CynixPub/CyMouse/assets/3d_board.png

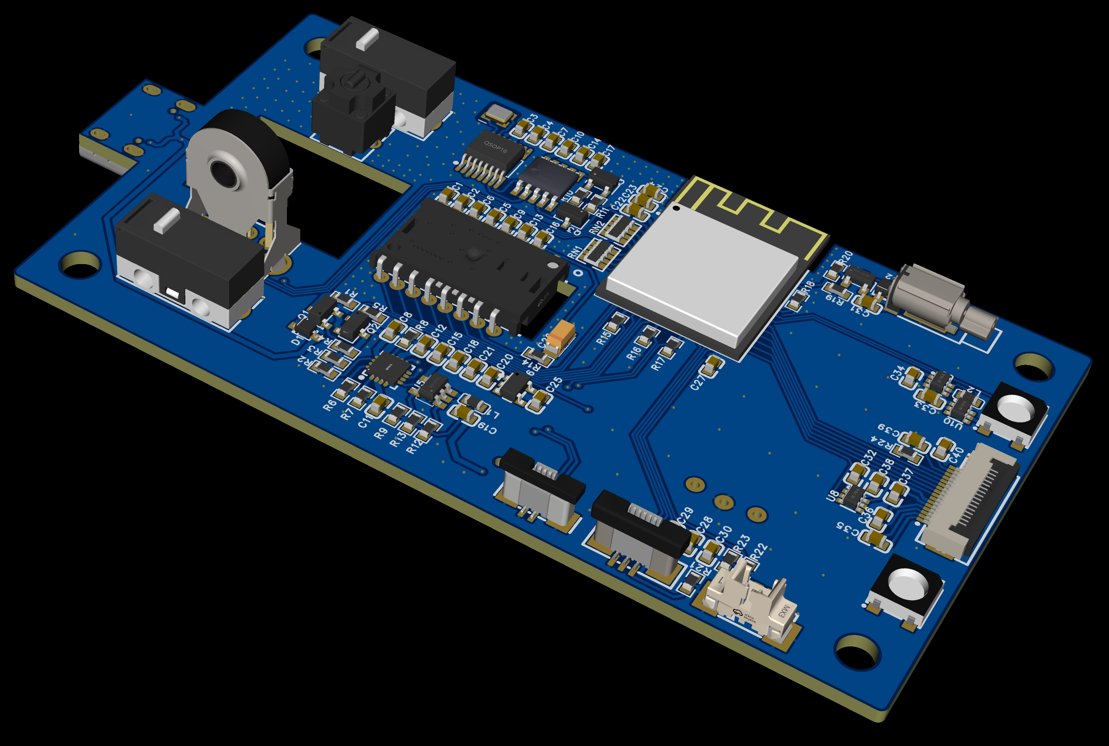
assets/3d_board.png
