CynixPub/CyMouse/assets/3d_model.png

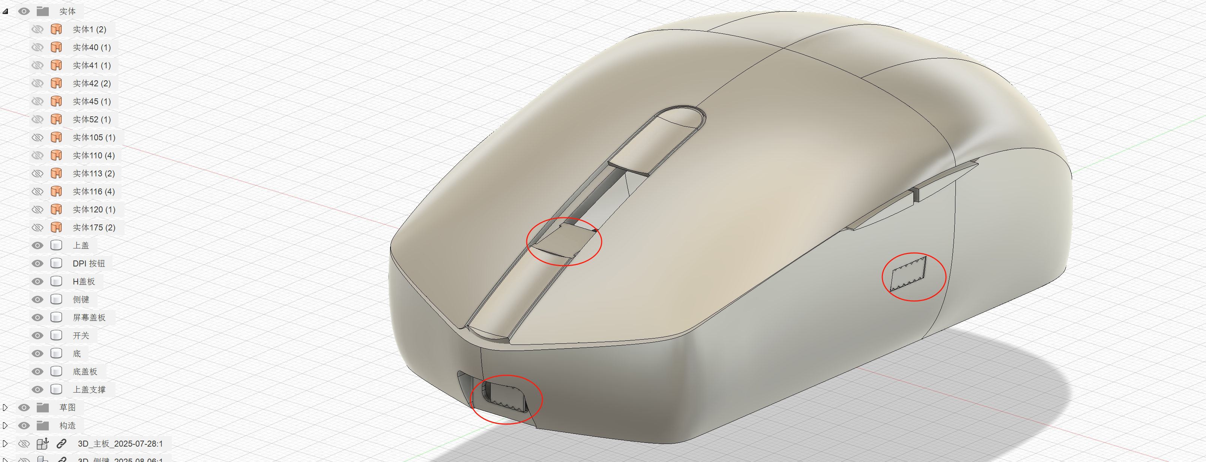
assets/3d_model.png
