CynixPub/CyMouse/assets/3d_model_1.png

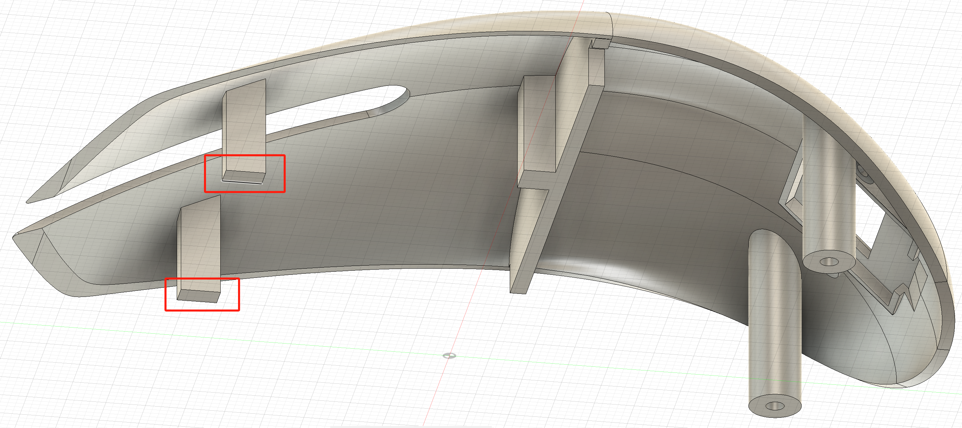
assets/3d_model_1.png
