CynixPub/CyMouse/assets/3d_model_2.png

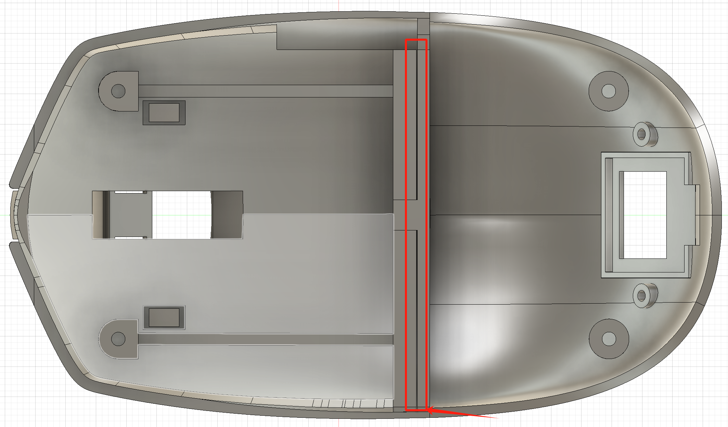
assets/3d_model_2.png
