CynixPub/CyMouse/assets/m1.2-1.5-2.png

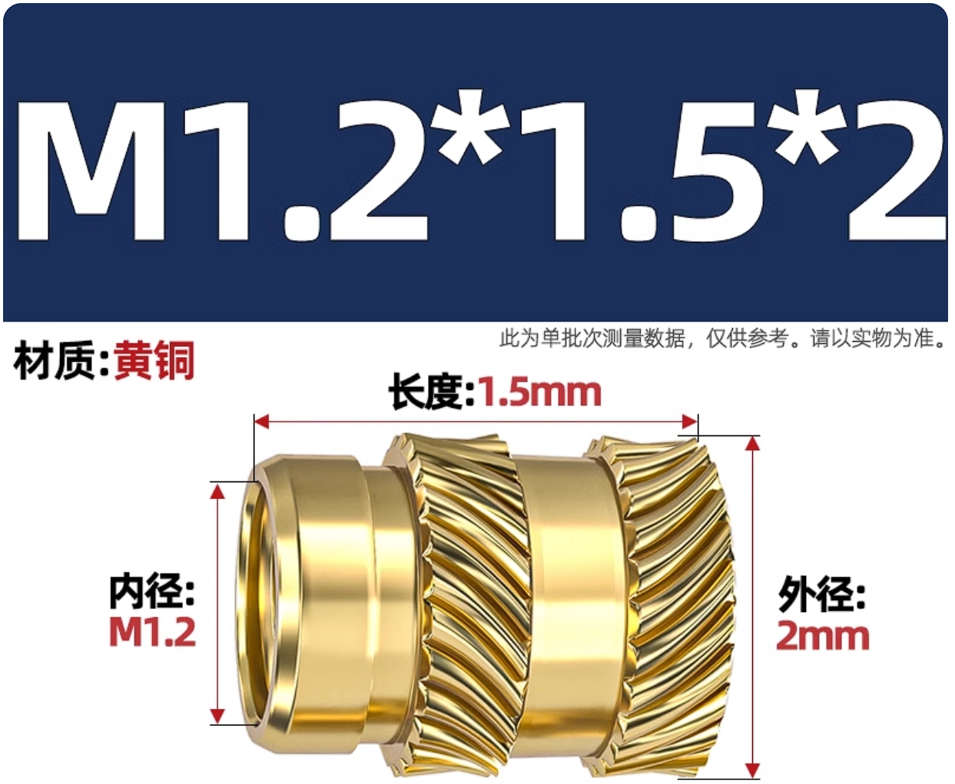
assets/m1.2-1.5-2.png
