CynixPub/CyMouse/assets/m1.6-3-2.5.png

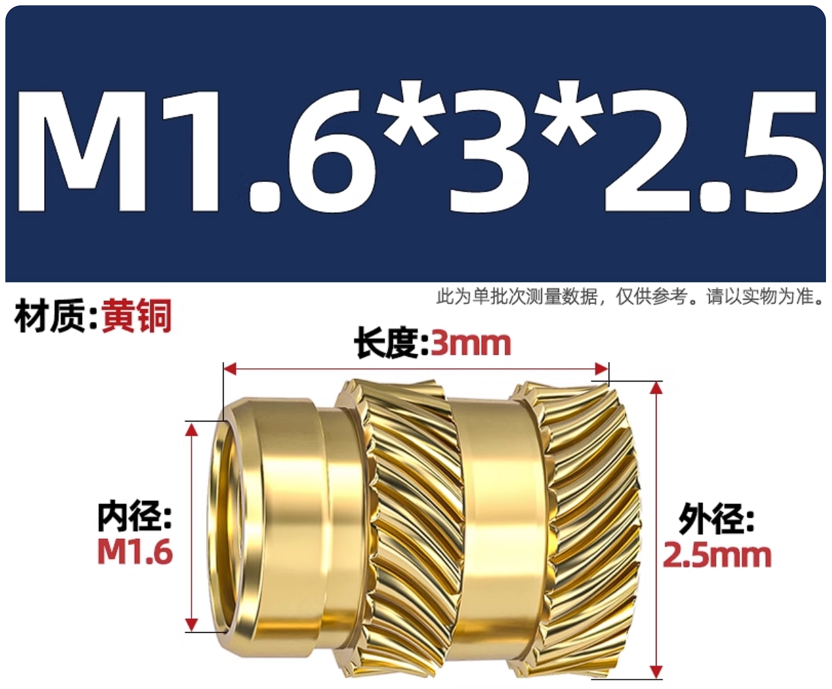
assets/m1.6-3-2.5.png
