CynixPub/CyMouse/assets/PCB.png

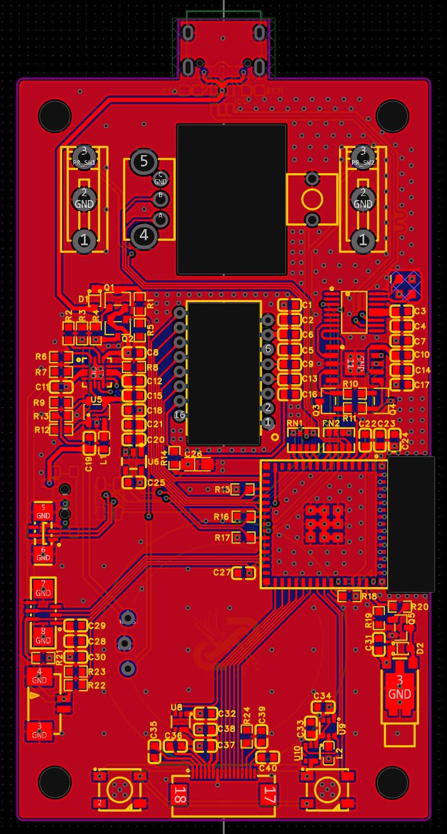
assets/PCB.png
