CynixPub/CyMouse/assets/view1.jpg

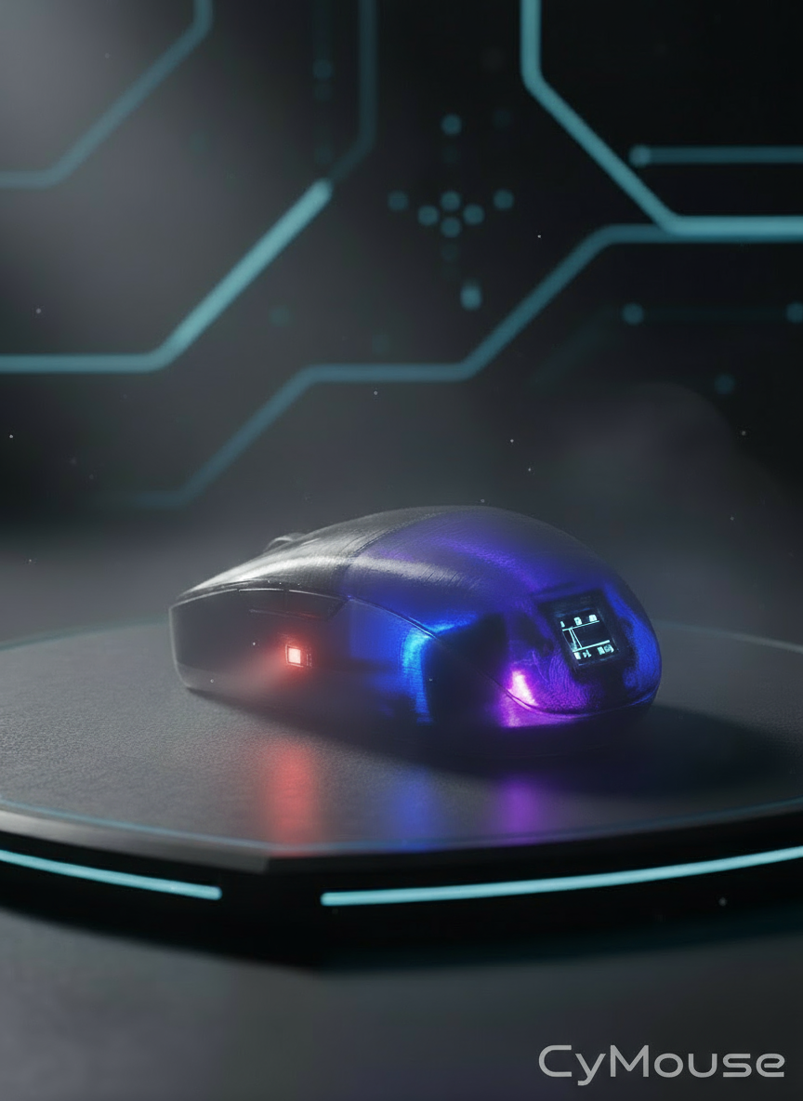
assets/view1.jpg
