CynixPub/CyMouse/assets/wx21.png

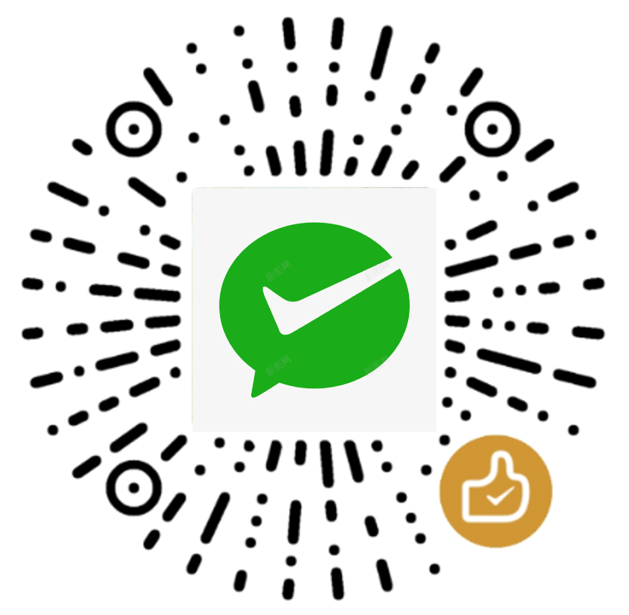
assets/wx21.png
