CynixPub/CyMouse/assets/主板.jpg

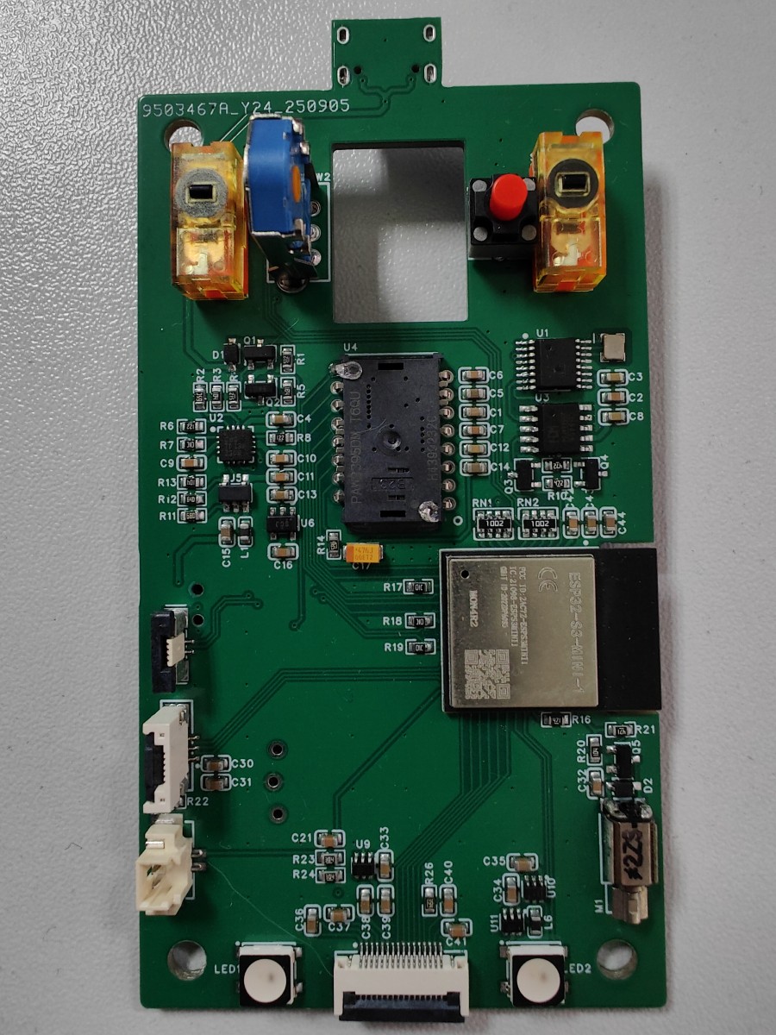
assets/主板.jpg
