CynixPub/CyMouse/assets/原理图.png

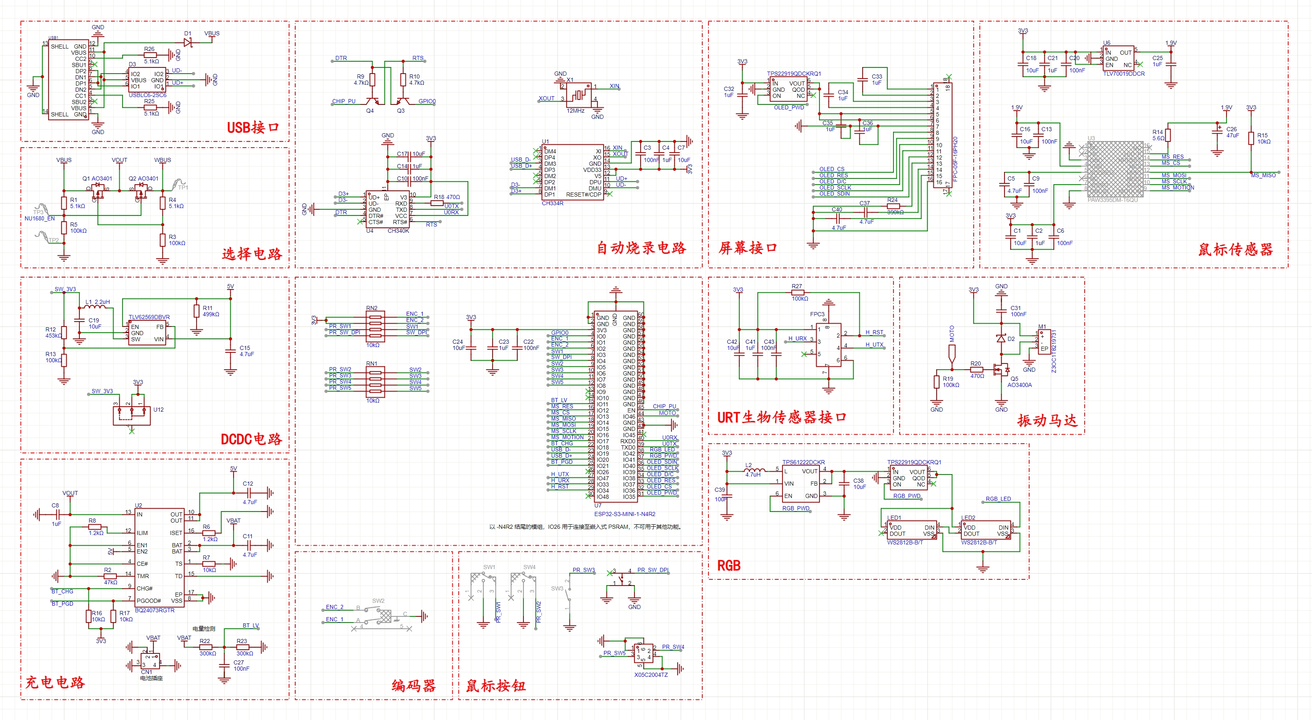
assets/原理图.png
