CynixPub/CyMouse/assets/电池.png

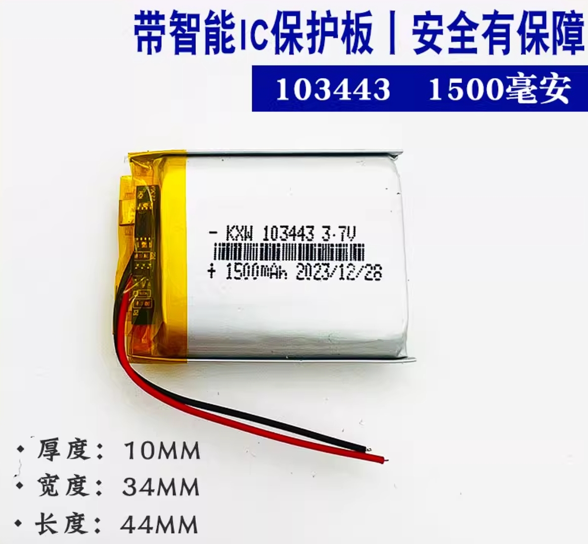
assets/电池.png
