CynixPub/CyMouse/flash_download_tool/1.png

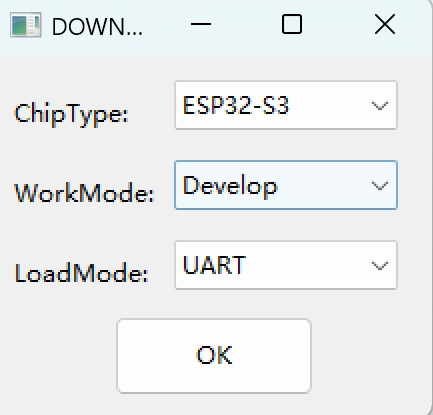
flash_download_tool/1.png
