CynixPub/CyMouse/flash_download_tool/2.png

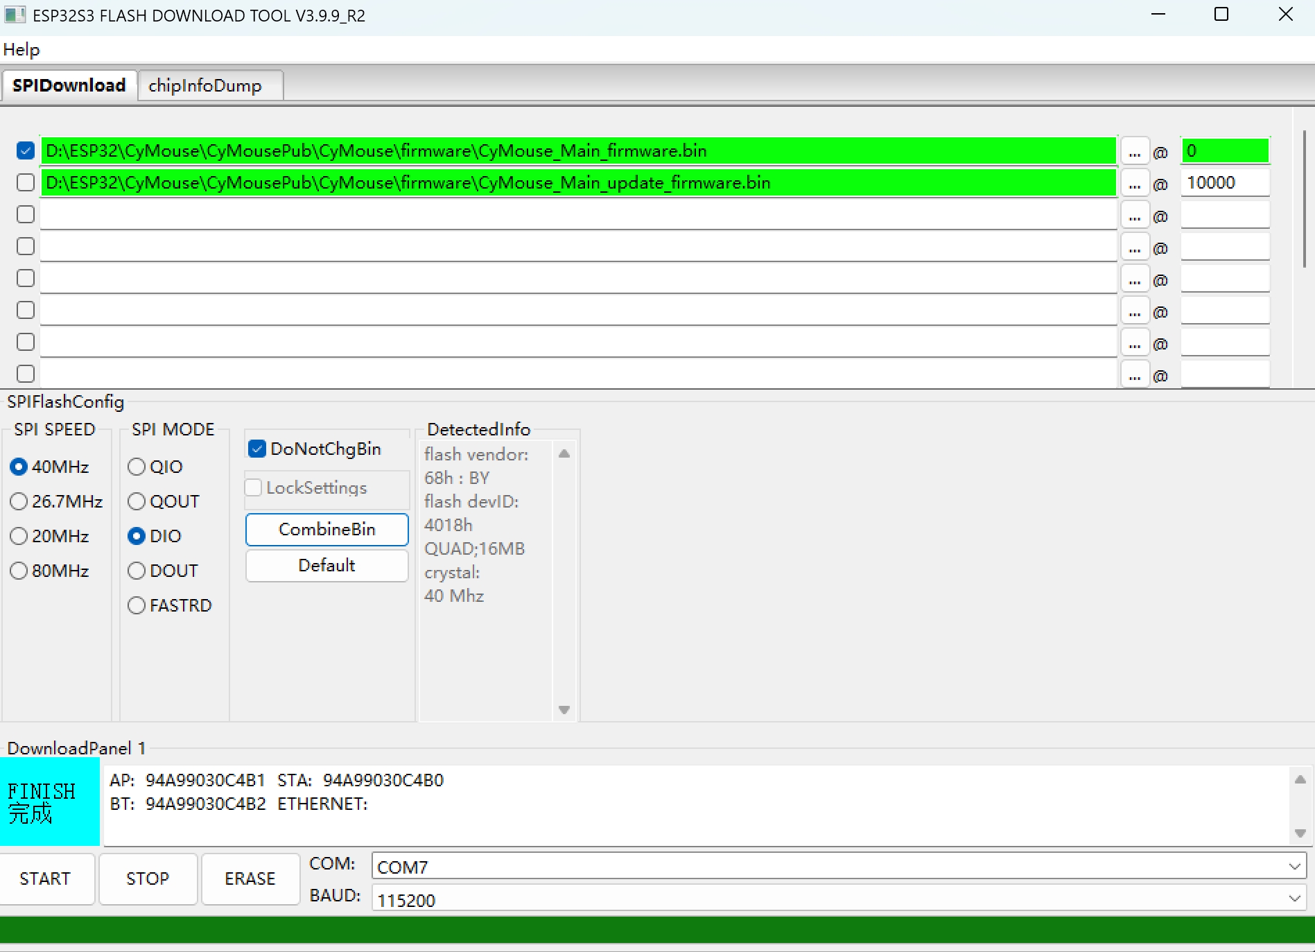
flash_download_tool/2.png
