CynixPub/CyMouse/assets/ble_test/interval_vs_Time.png

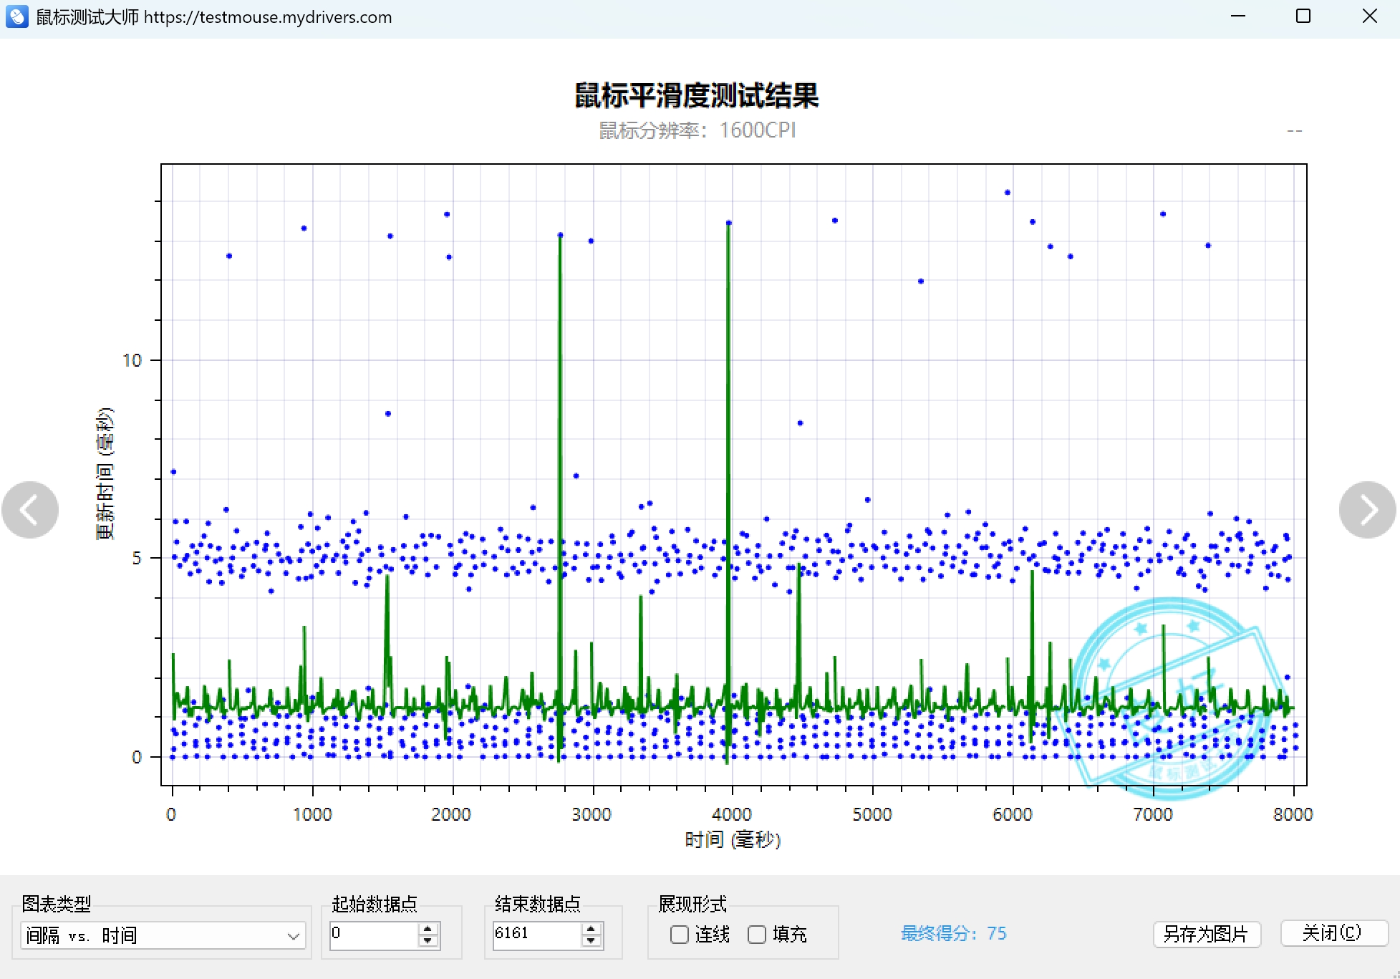
assets/ble_test/interval_vs_Time.png
