CynixPub/CyMouse/assets/ble_test/polling_rate.png

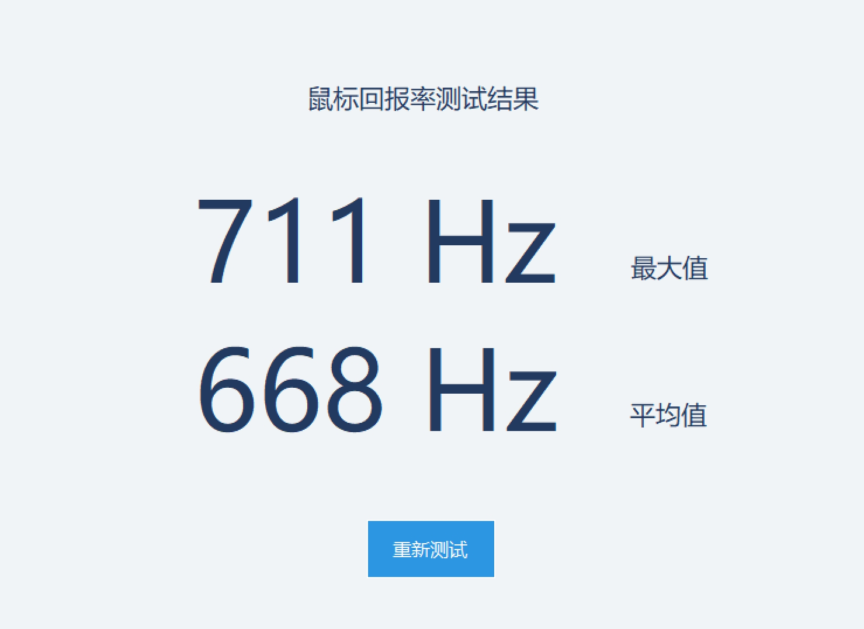
assets/ble_test/polling_rate.png
