CynixPub/CyMouse/assets/ble_test/x_vs_y.png

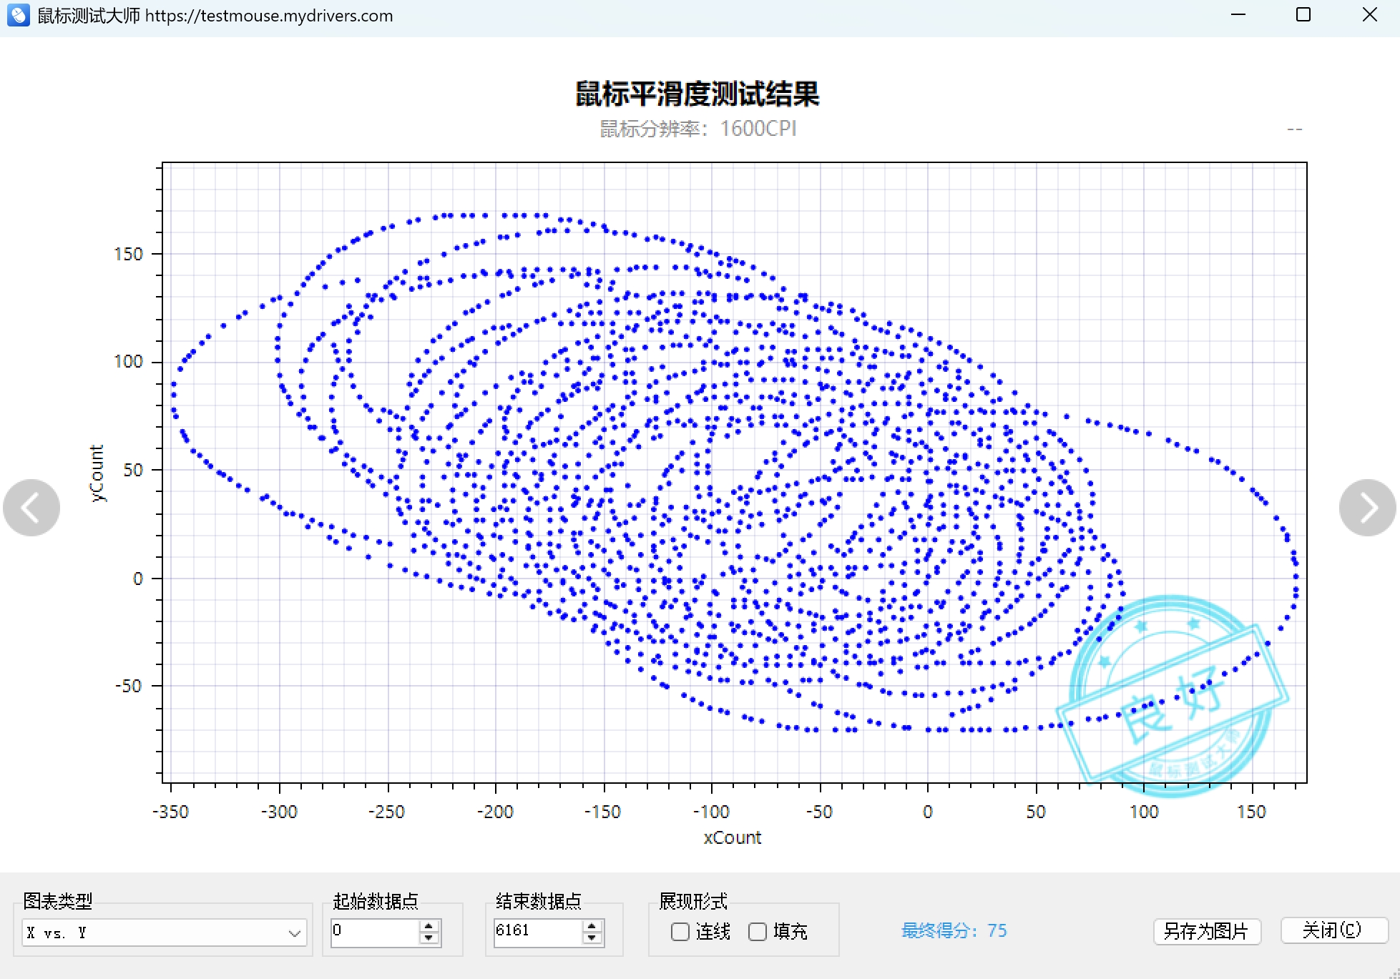
assets/ble_test/x_vs_y.png
