CynixPub/CyMouse/assets/ble_test/xCount_vs_Time.png

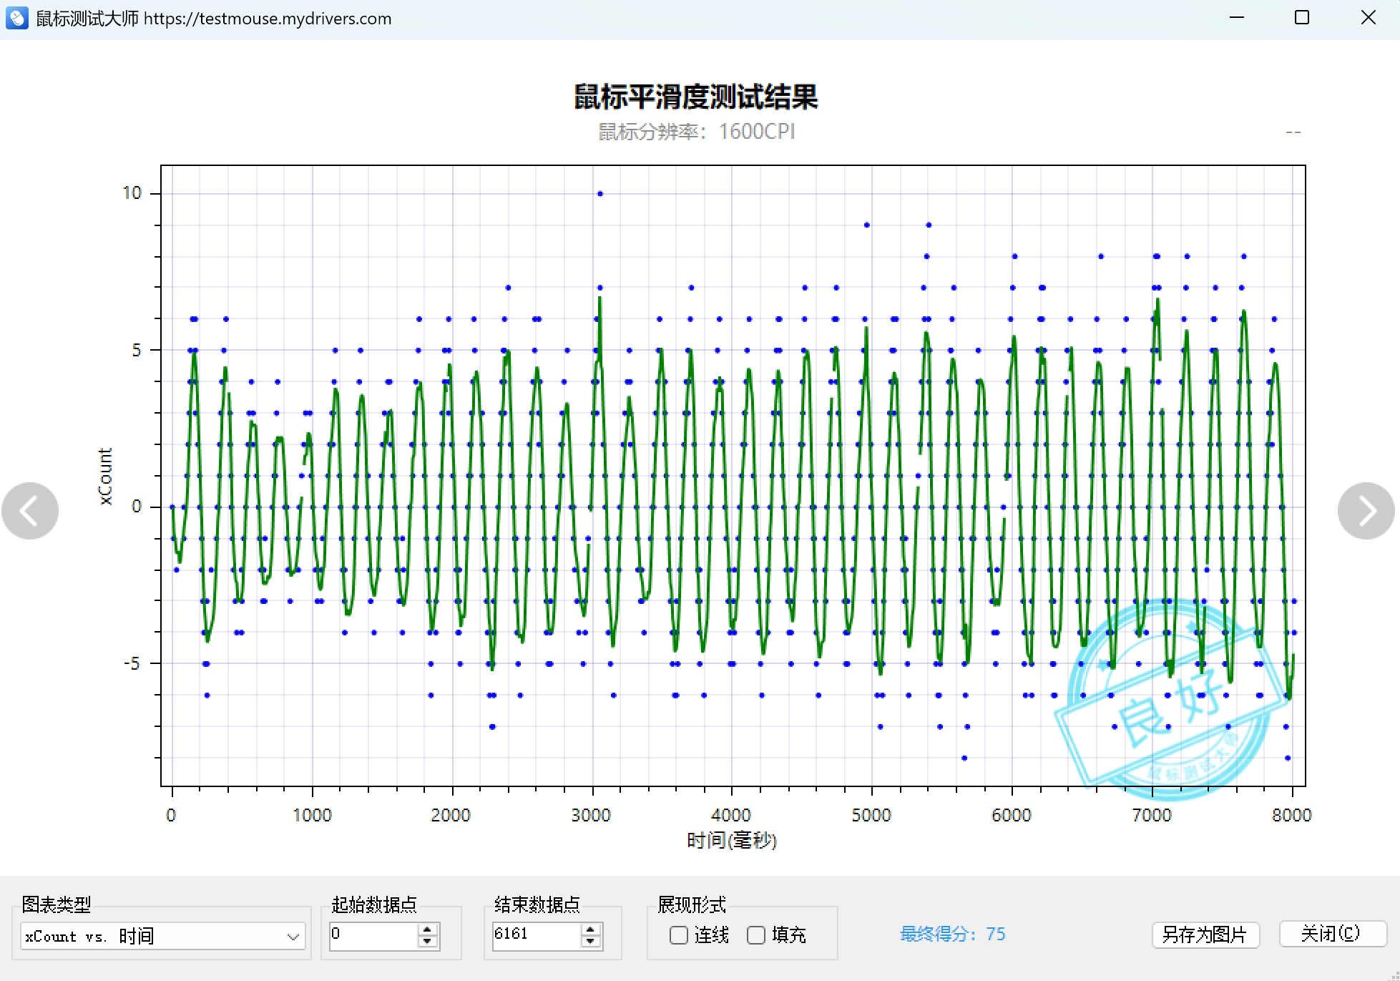
assets/ble_test/xCount_vs_Time.png
