CynixPub/CyMouse/assets/ble_test/xySpeed_vs_Time.png

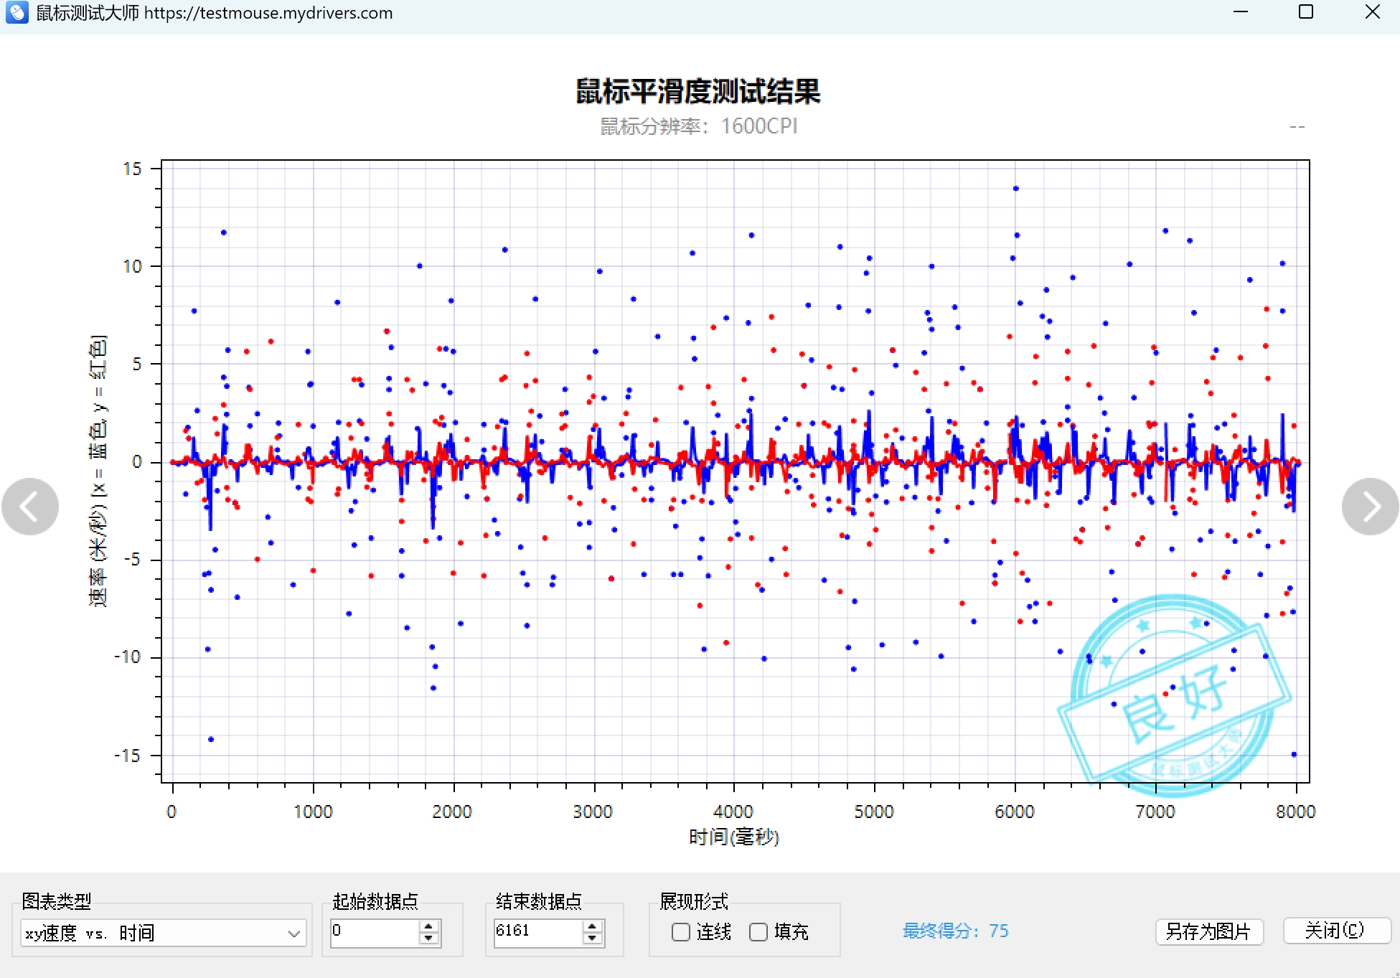
assets/ble_test/xySpeed_vs_Time.png
