CynixPub/CyMouse/assets/ble_test/ySpeed_vs_Time.png

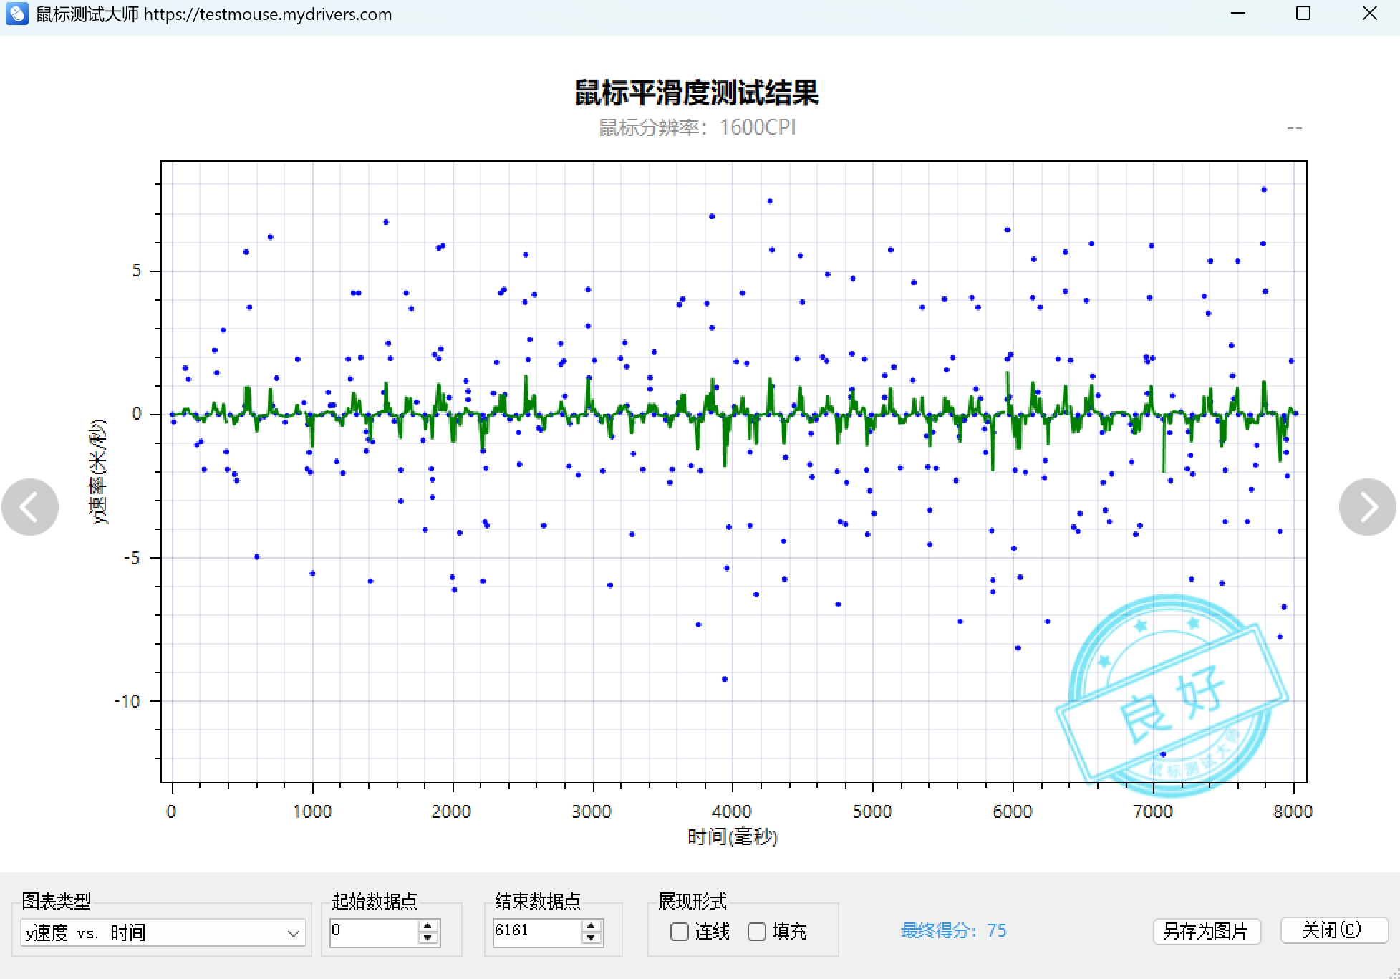
assets/ble_test/ySpeed_vs_Time.png
