CynixPub/CyMouse/assets/esp-now_test/interval_vs_Time.png

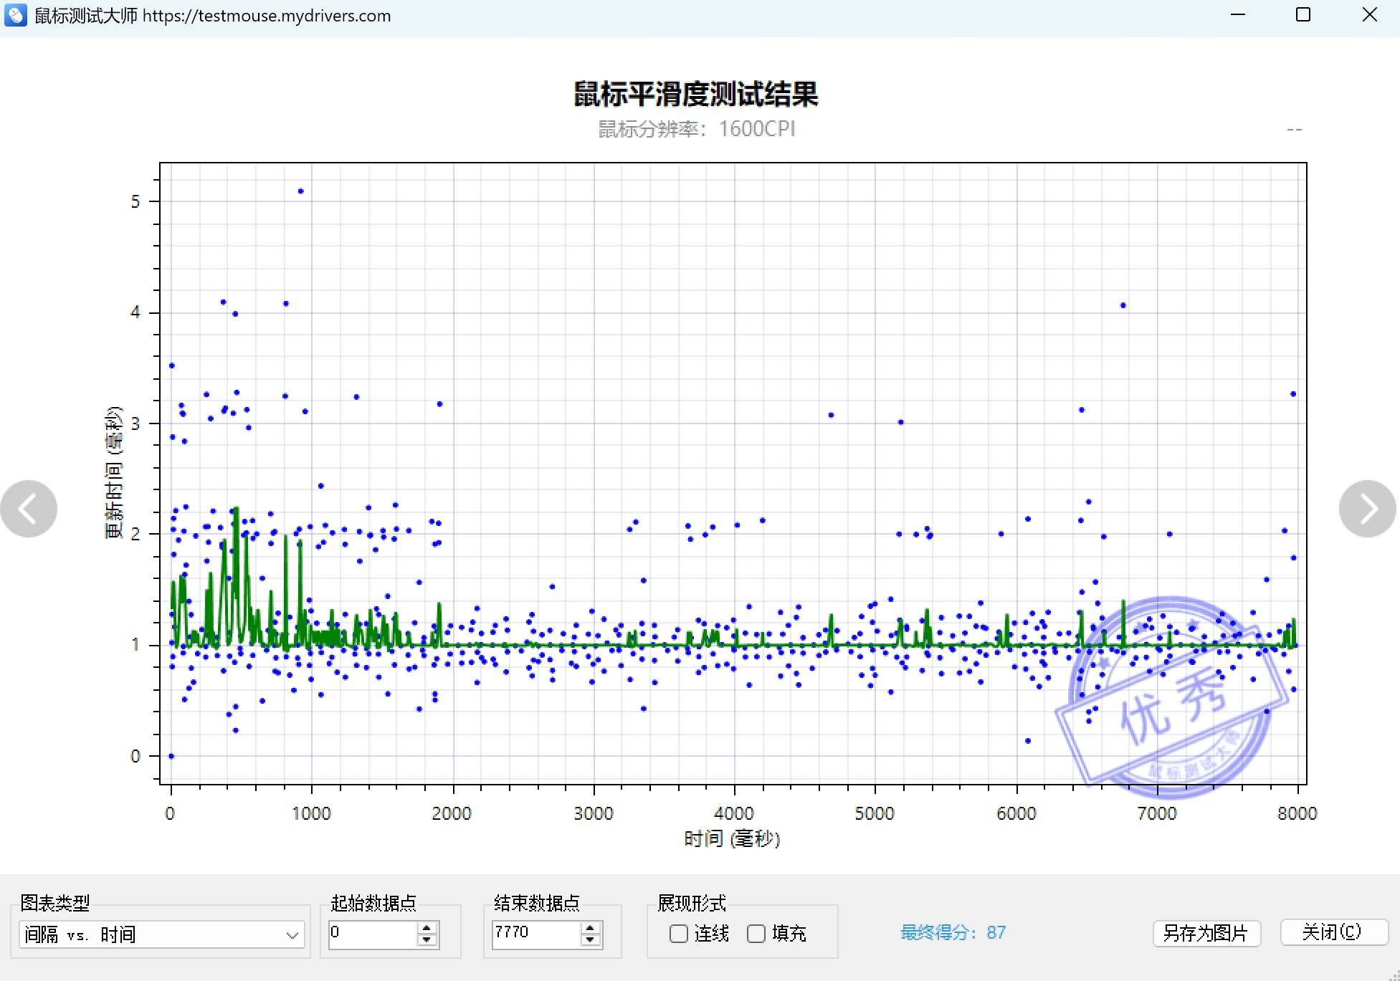
assets/esp-now_test/interval_vs_Time.png
