CynixPub/CyMouse/assets/esp-now_test/X_vs_Y.png

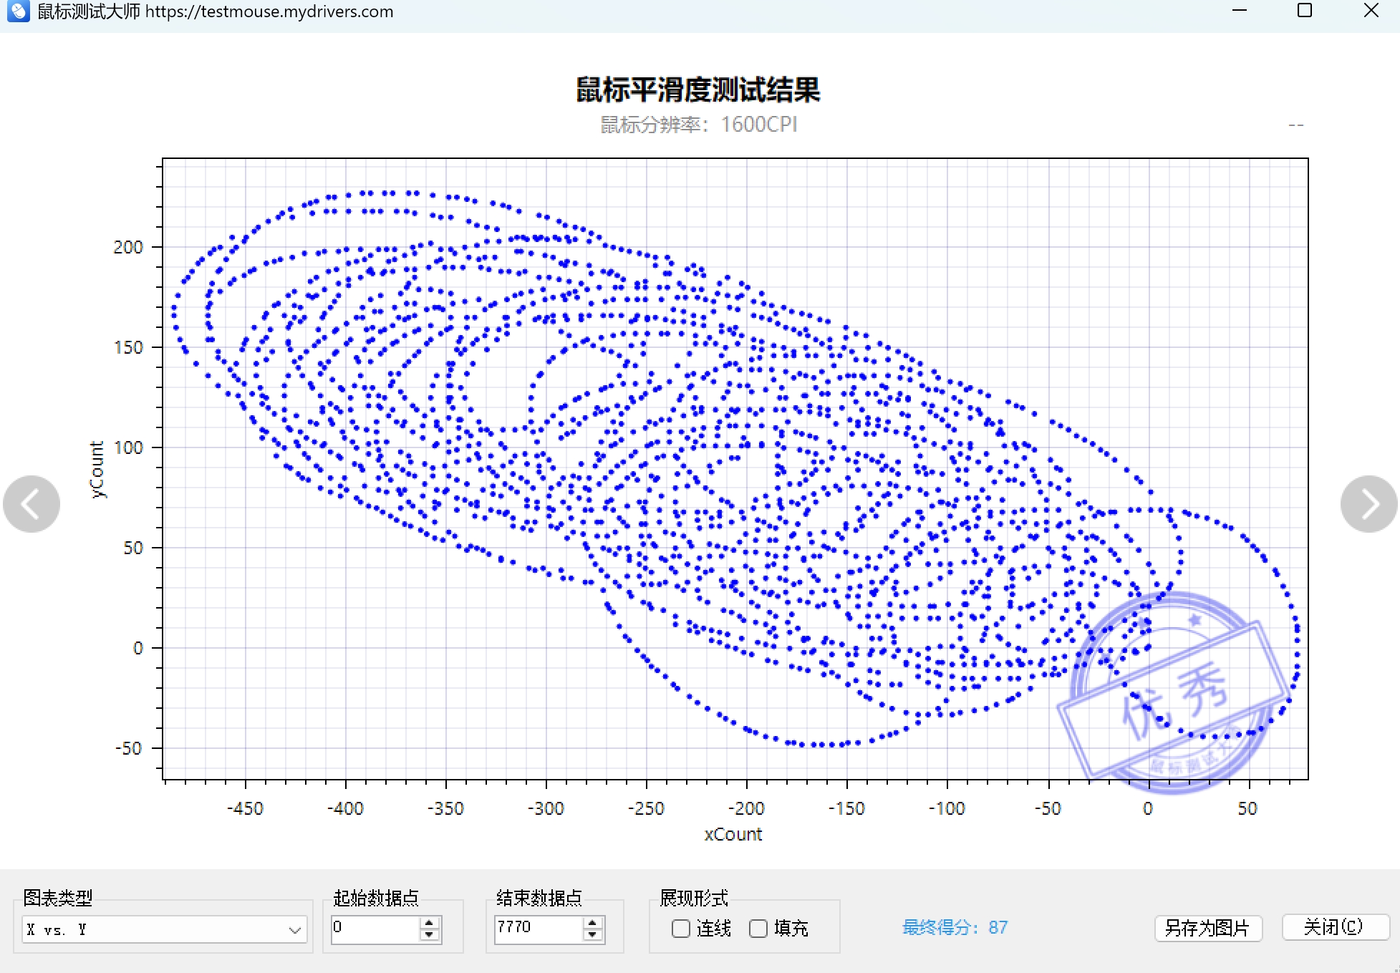
assets/esp-now_test/X_vs_Y.png
