CynixPub/CyMouse/assets/esp-now_test/xSpeed_vs_Time.png

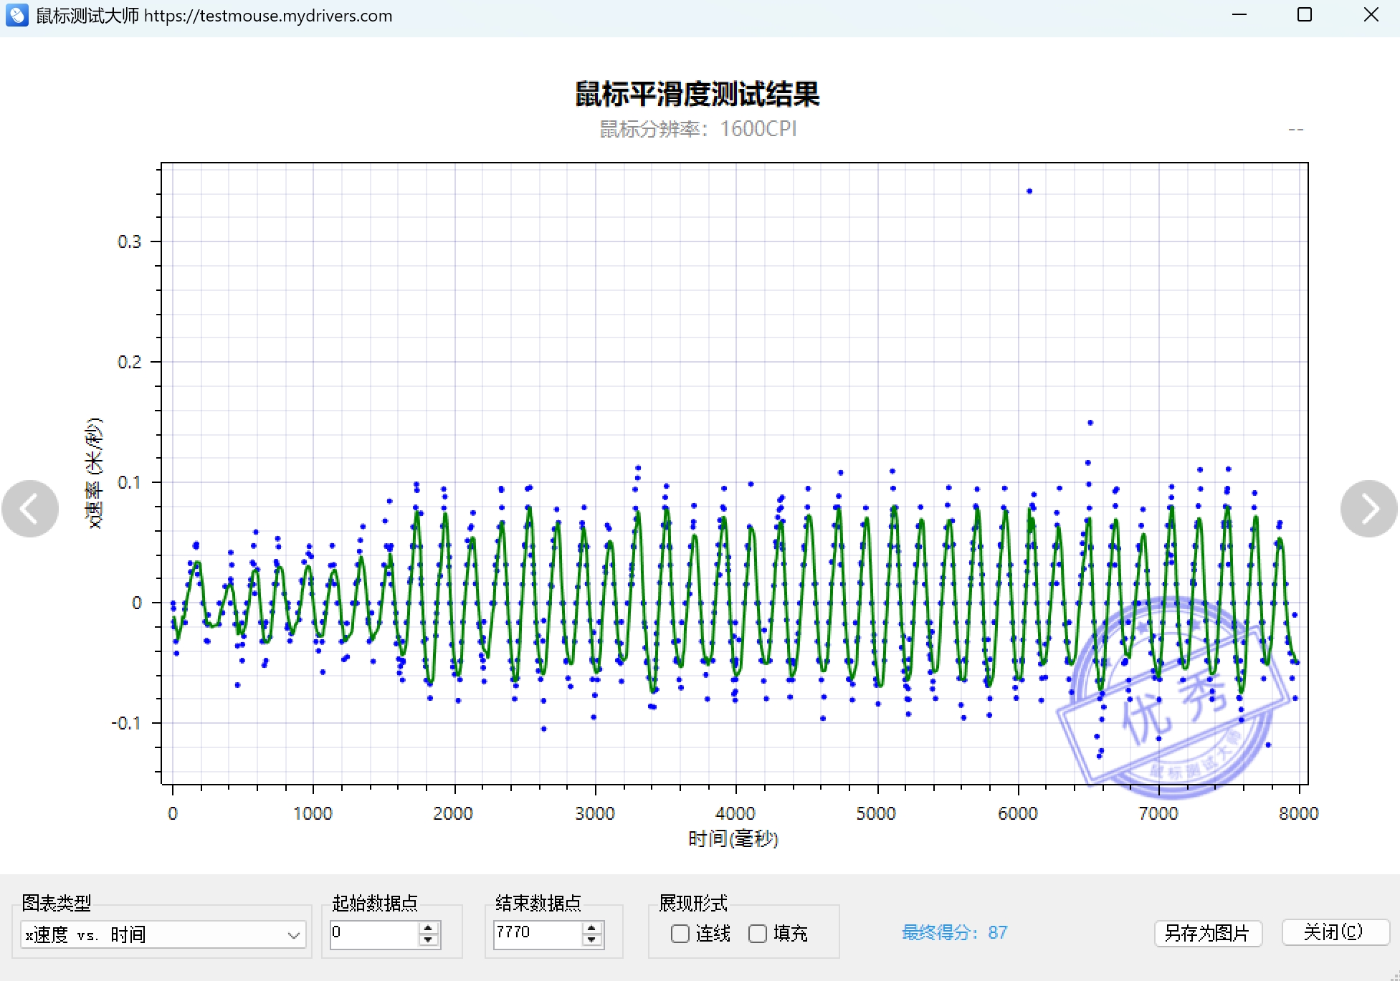
assets/esp-now_test/xSpeed_vs_Time.png
