CynixPub/CyMouse/assets/esp-now_test/xySpeed_vs_Time.png

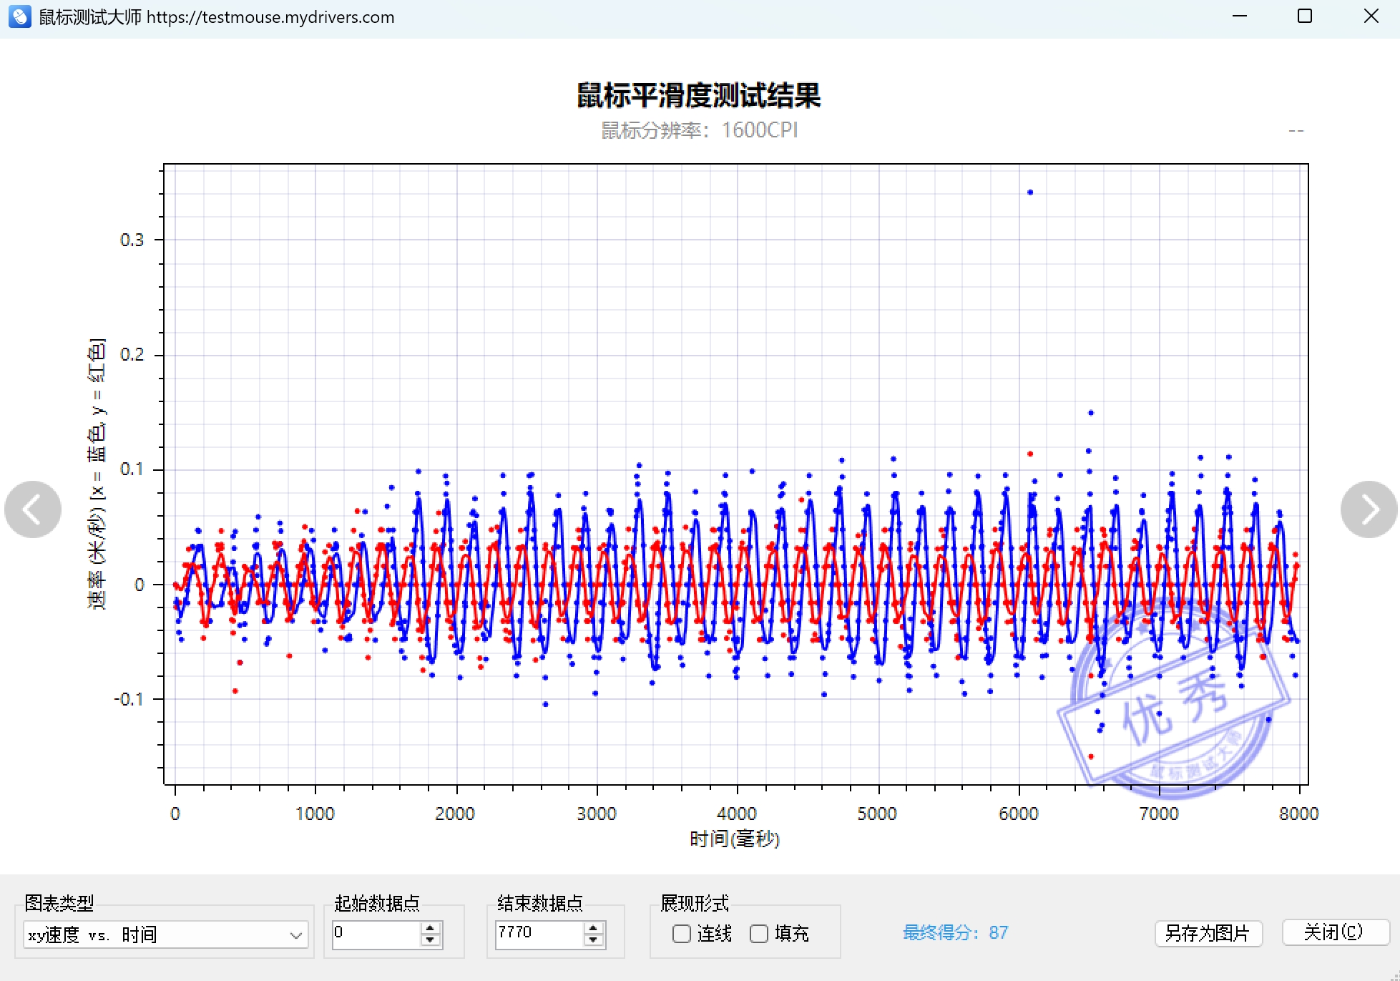
assets/esp-now_test/xySpeed_vs_Time.png
