CynixPub/CyMouse/assets/esp-now_test/yCount_vs_Time.png

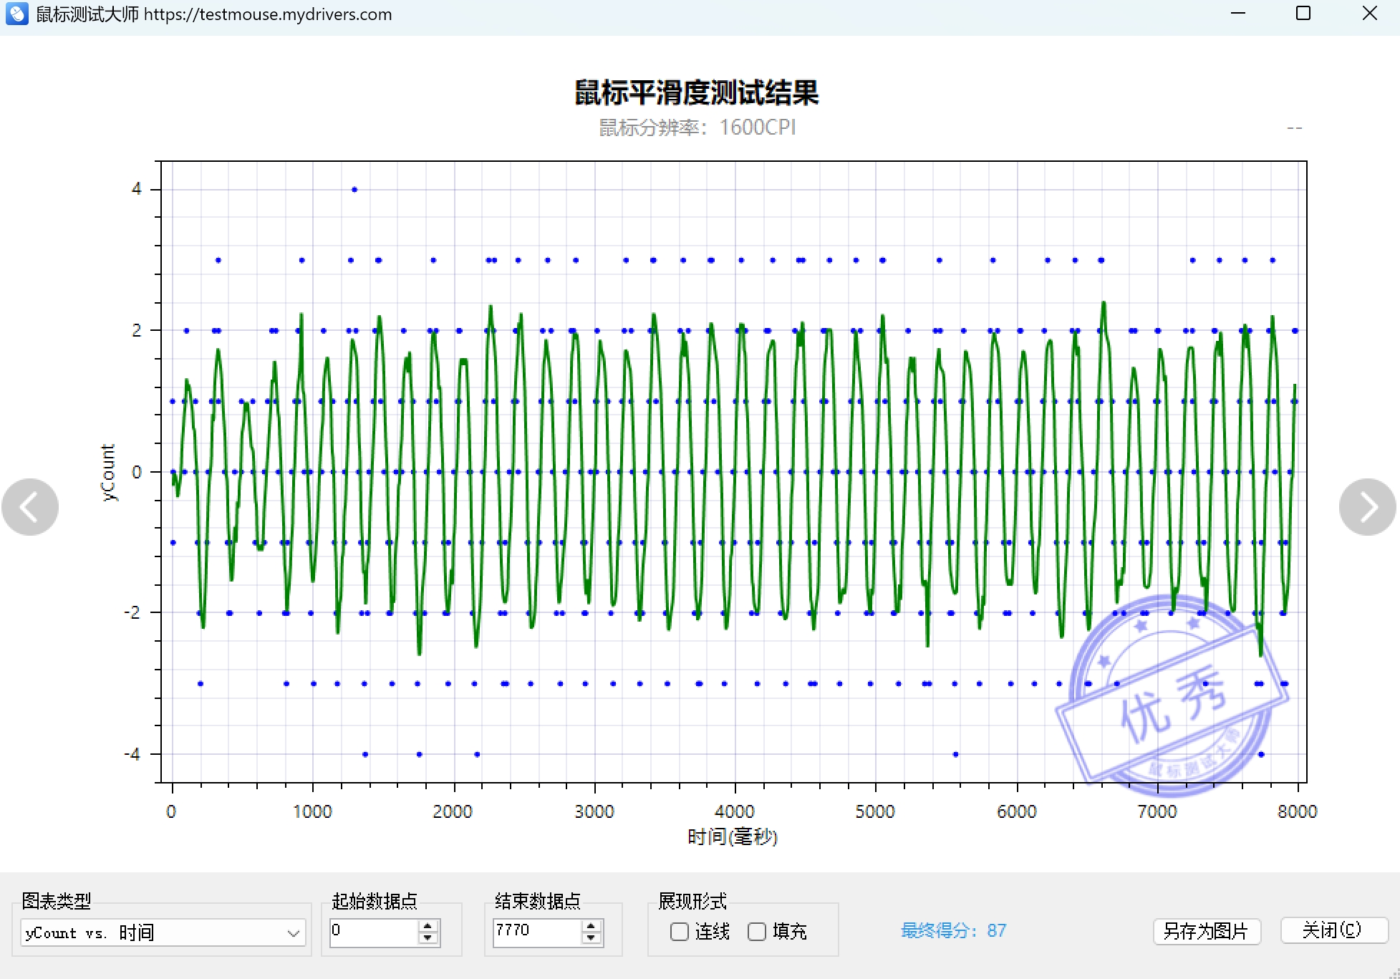
assets/esp-now_test/yCount_vs_Time.png
