CynixPub/CyMouse/assets/esp-now_test/ySpeed_vs_Time.png

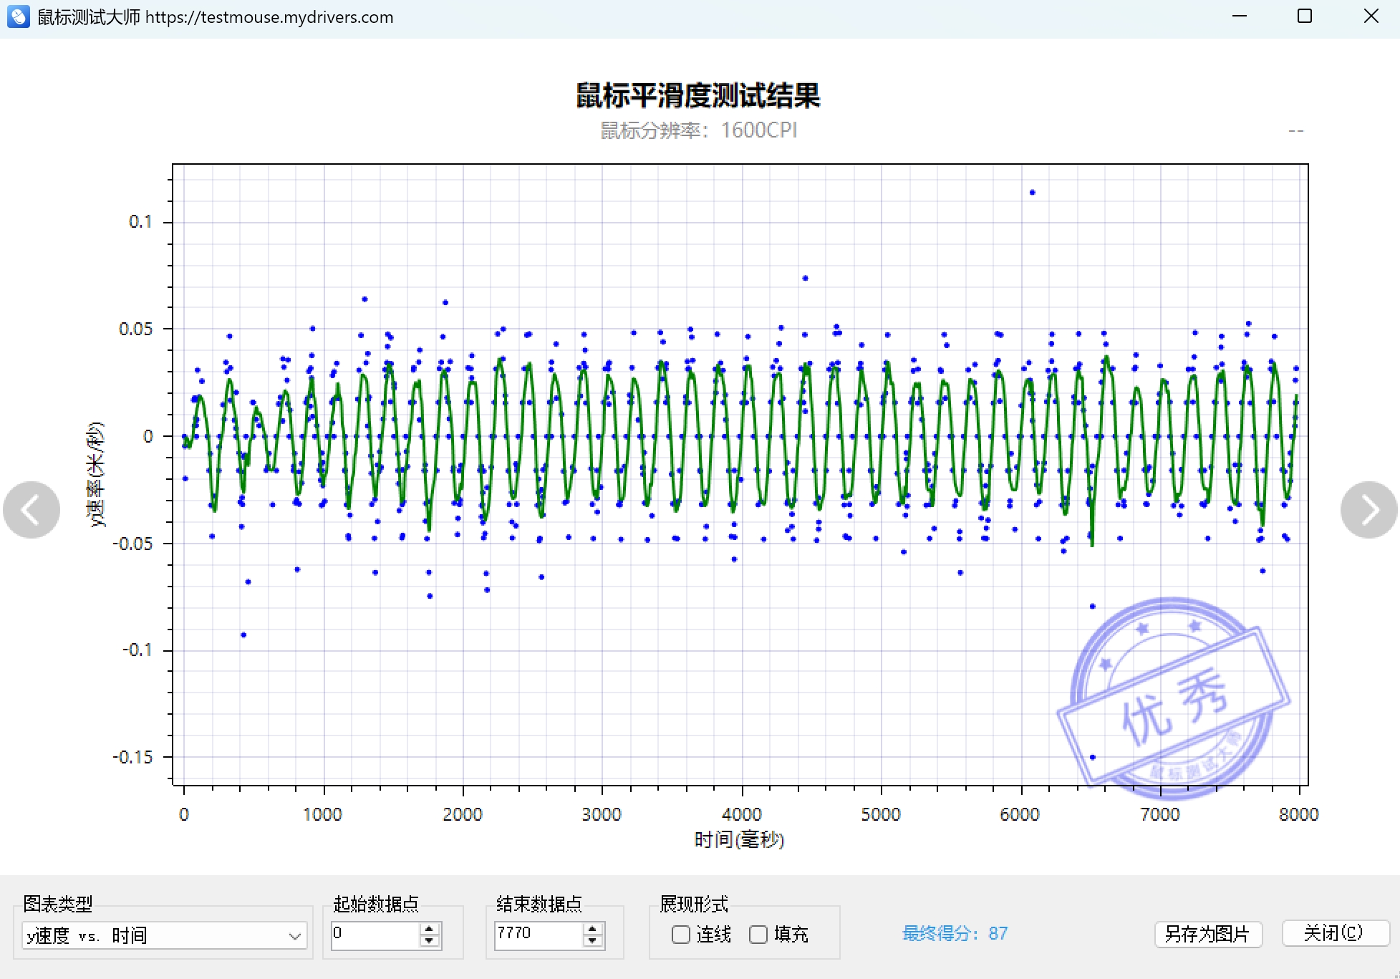
assets/esp-now_test/ySpeed_vs_Time.png
