CynixPub/CyMouse/assets/usb_test/interval_vs_Time.png

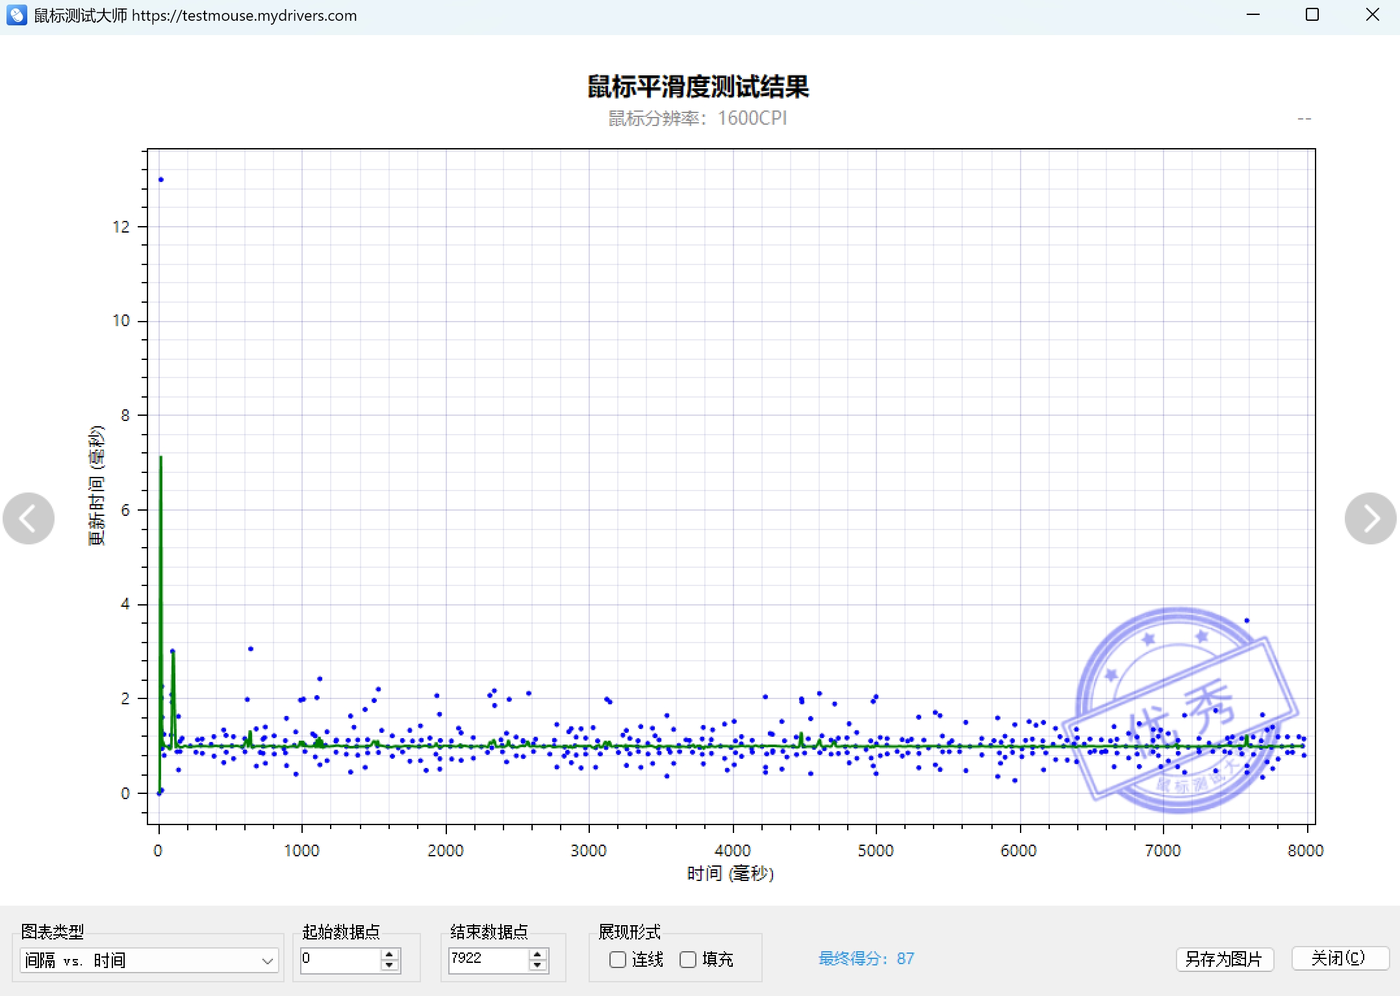
assets/usb_test/interval_vs_Time.png
