CynixPub/CyMouse/assets/usb_test/polling_rate.png

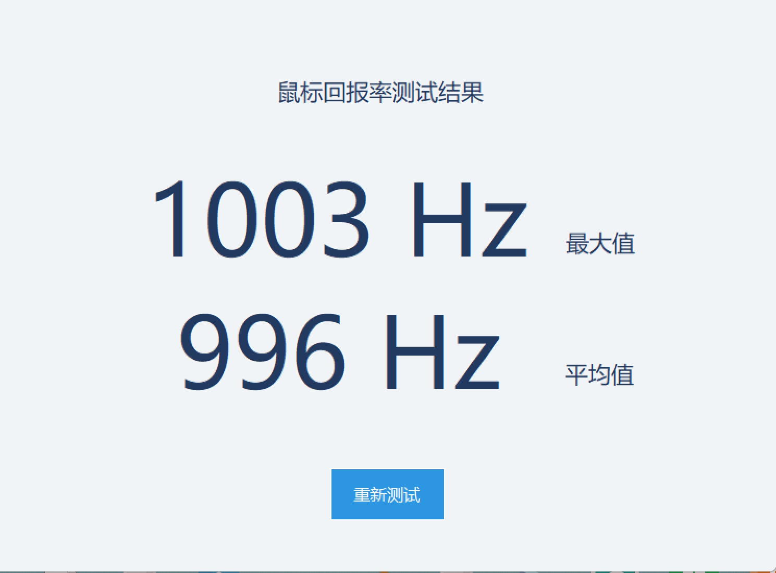
assets/usb_test/polling_rate.png
