CynixPub/CyMouse/assets/usb_test/xCount_vs_Time.png

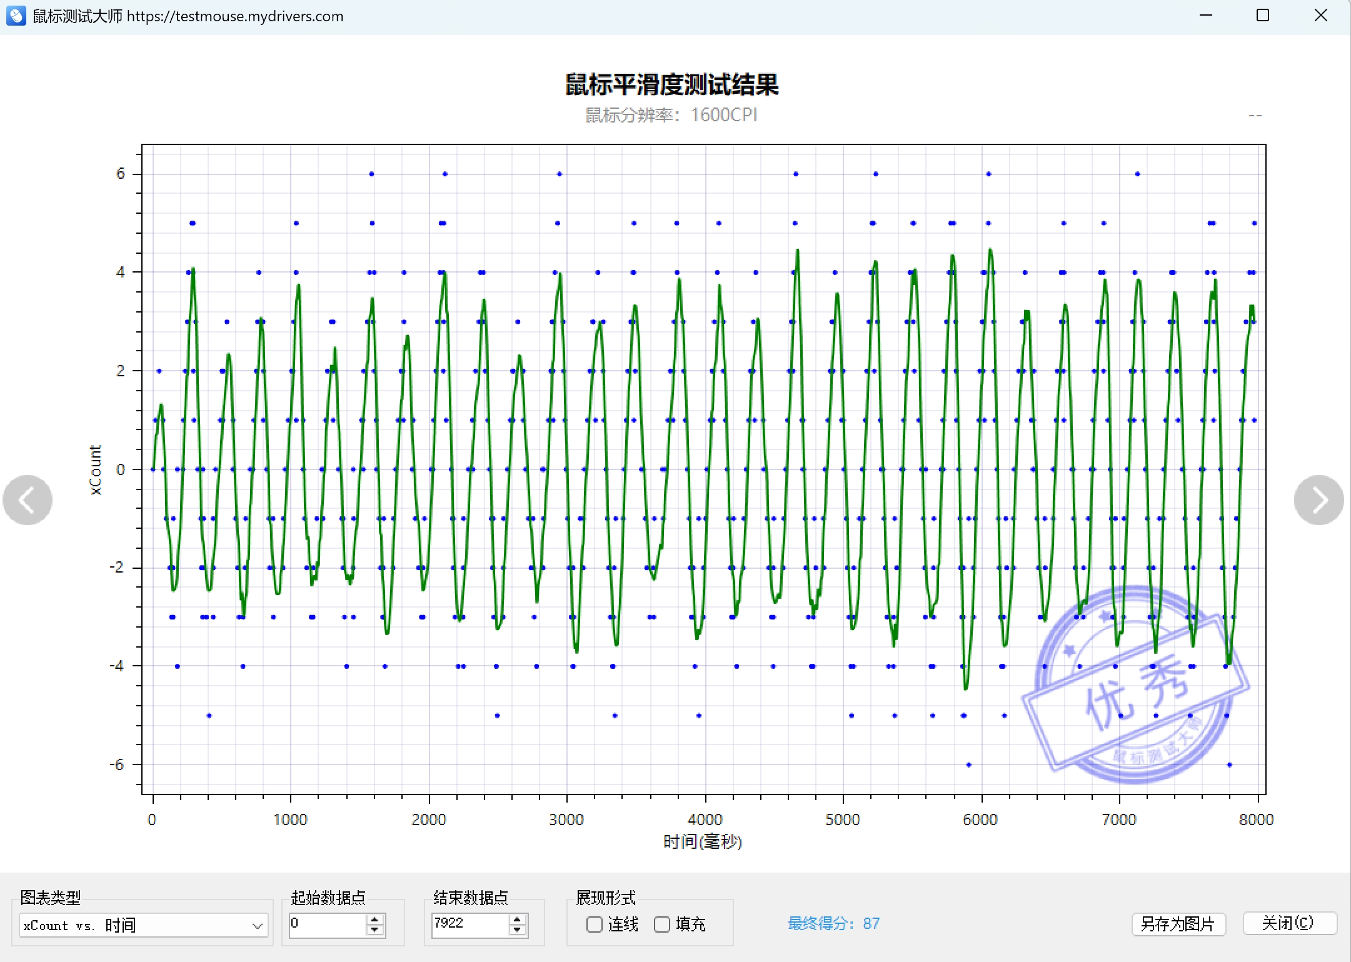
assets/usb_test/xCount_vs_Time.png
