CynixPub/CyMouse/assets/usb_test/xSpeed_vs_Time.png

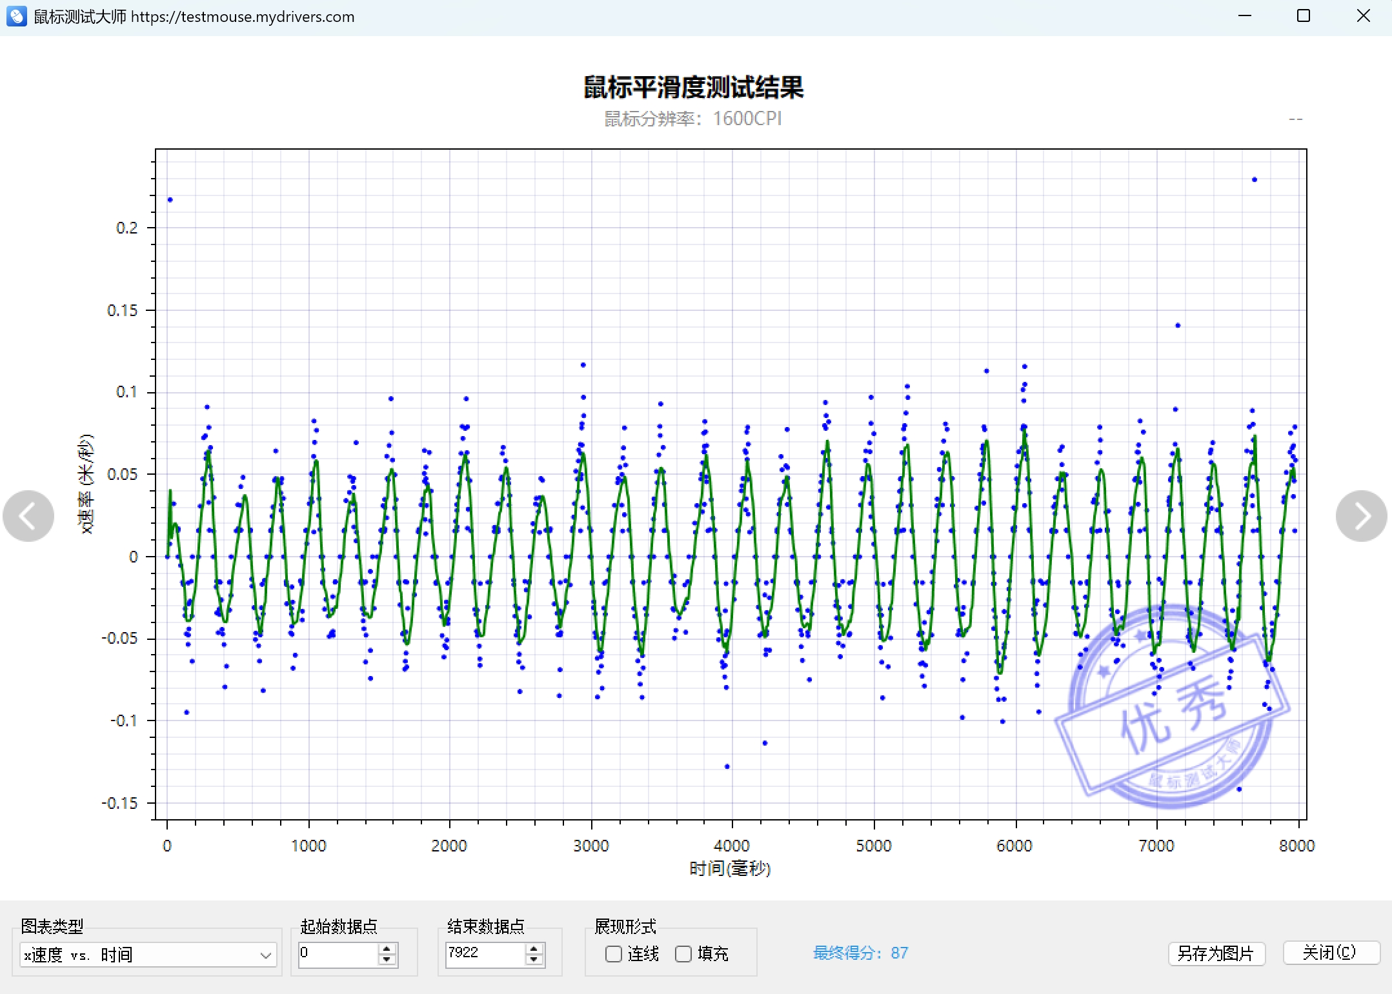
assets/usb_test/xSpeed_vs_Time.png
