CynixPub/CyMouse/assets/usb_test/xyCount_vs_Time.png

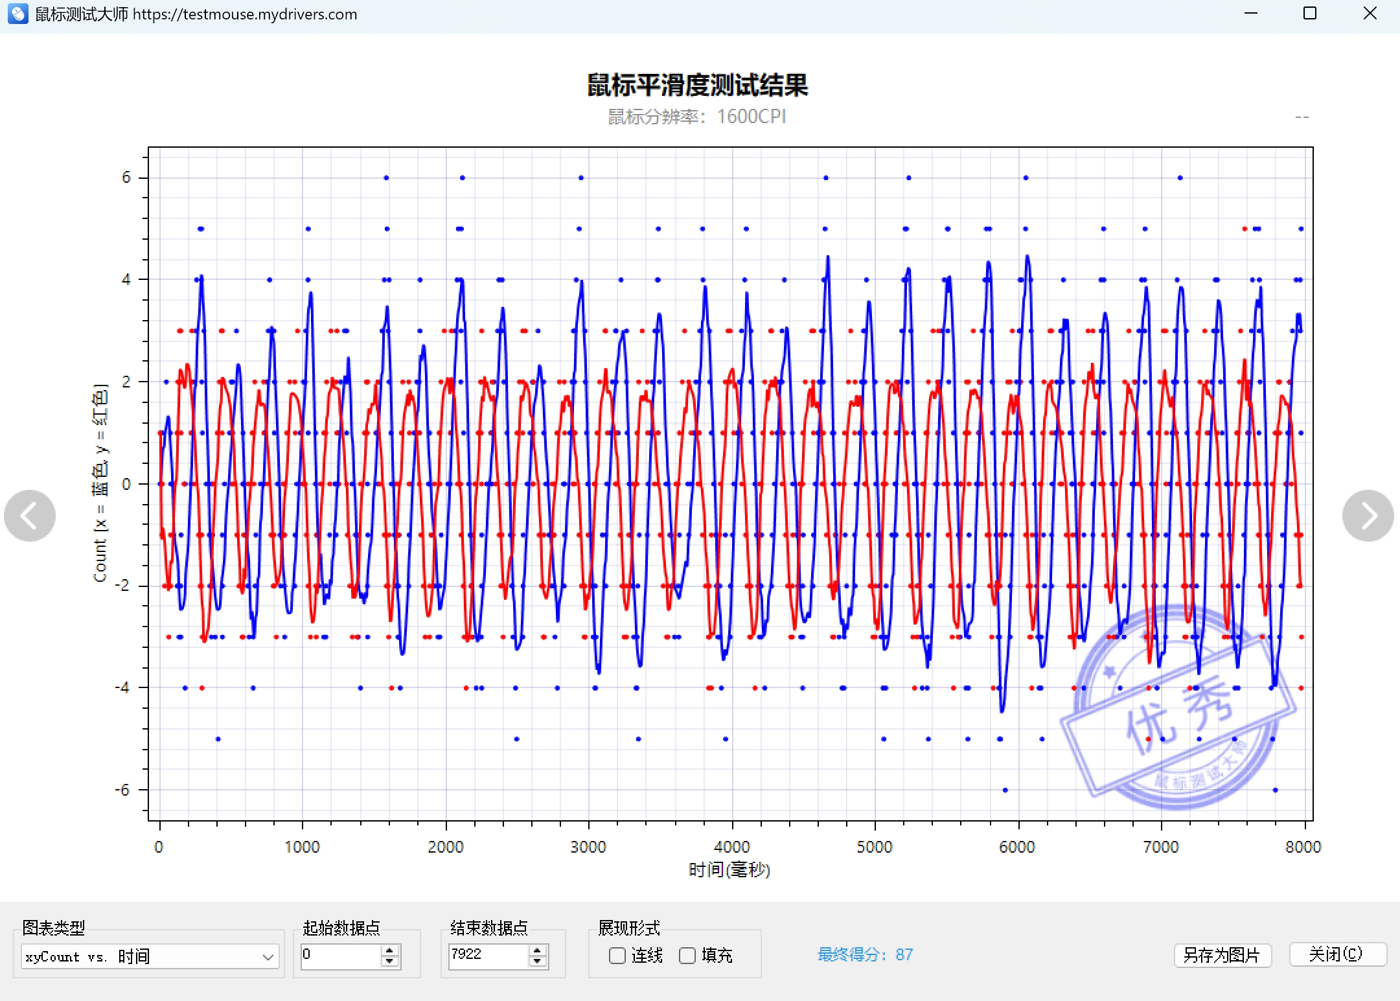
assets/usb_test/xyCount_vs_Time.png
