CynixPub/CyMouse/assets/usb_test/yCount_vs_Time.png

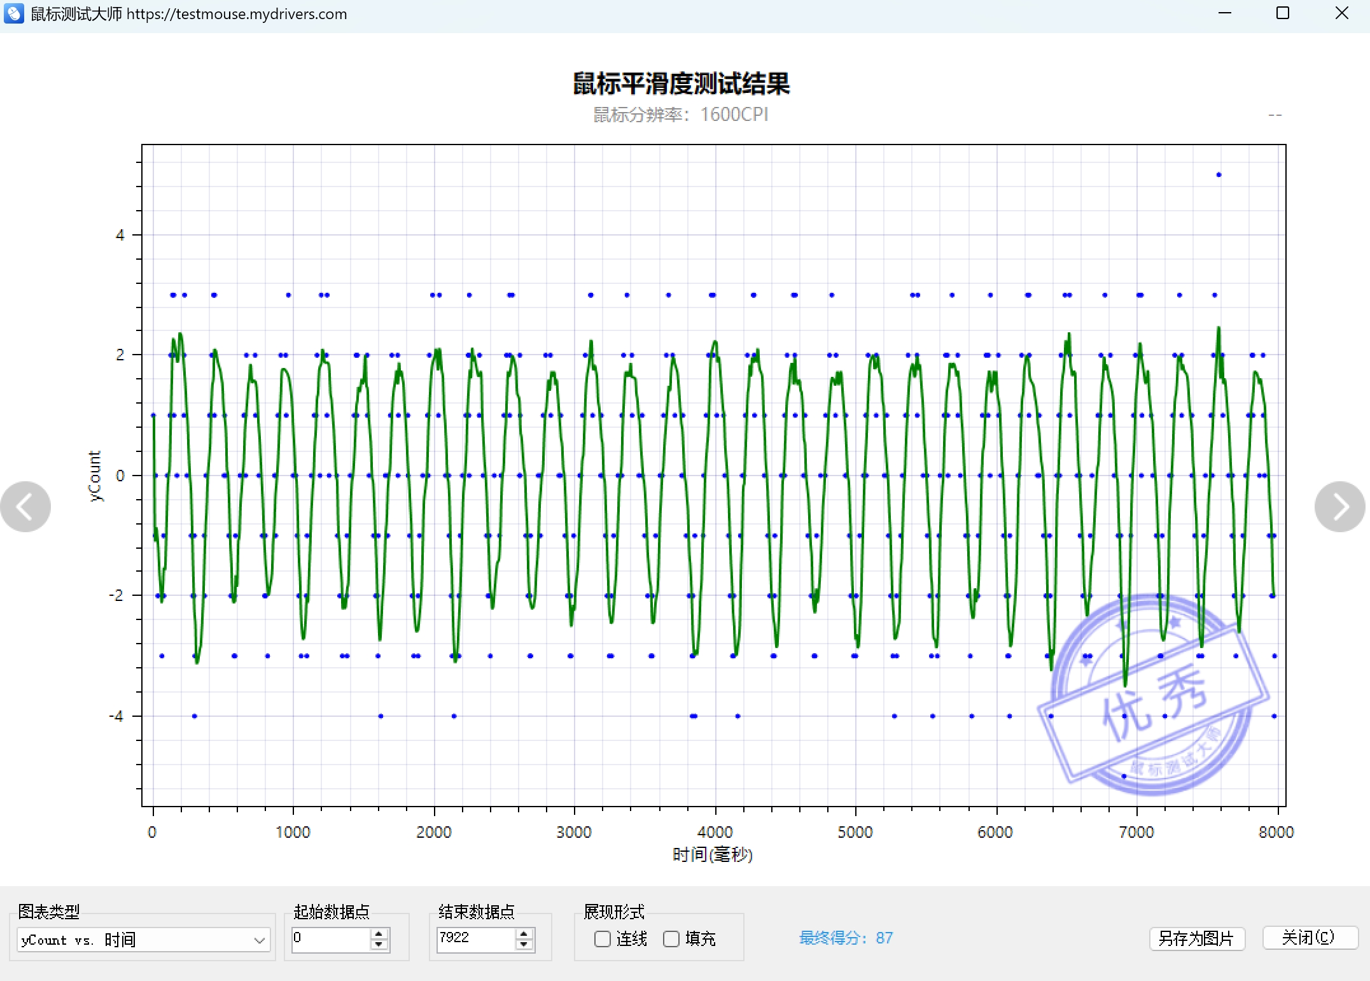
assets/usb_test/yCount_vs_Time.png
