CynixPub/CyMouse/assets/usb_test/ySpeed_vs_Time.png

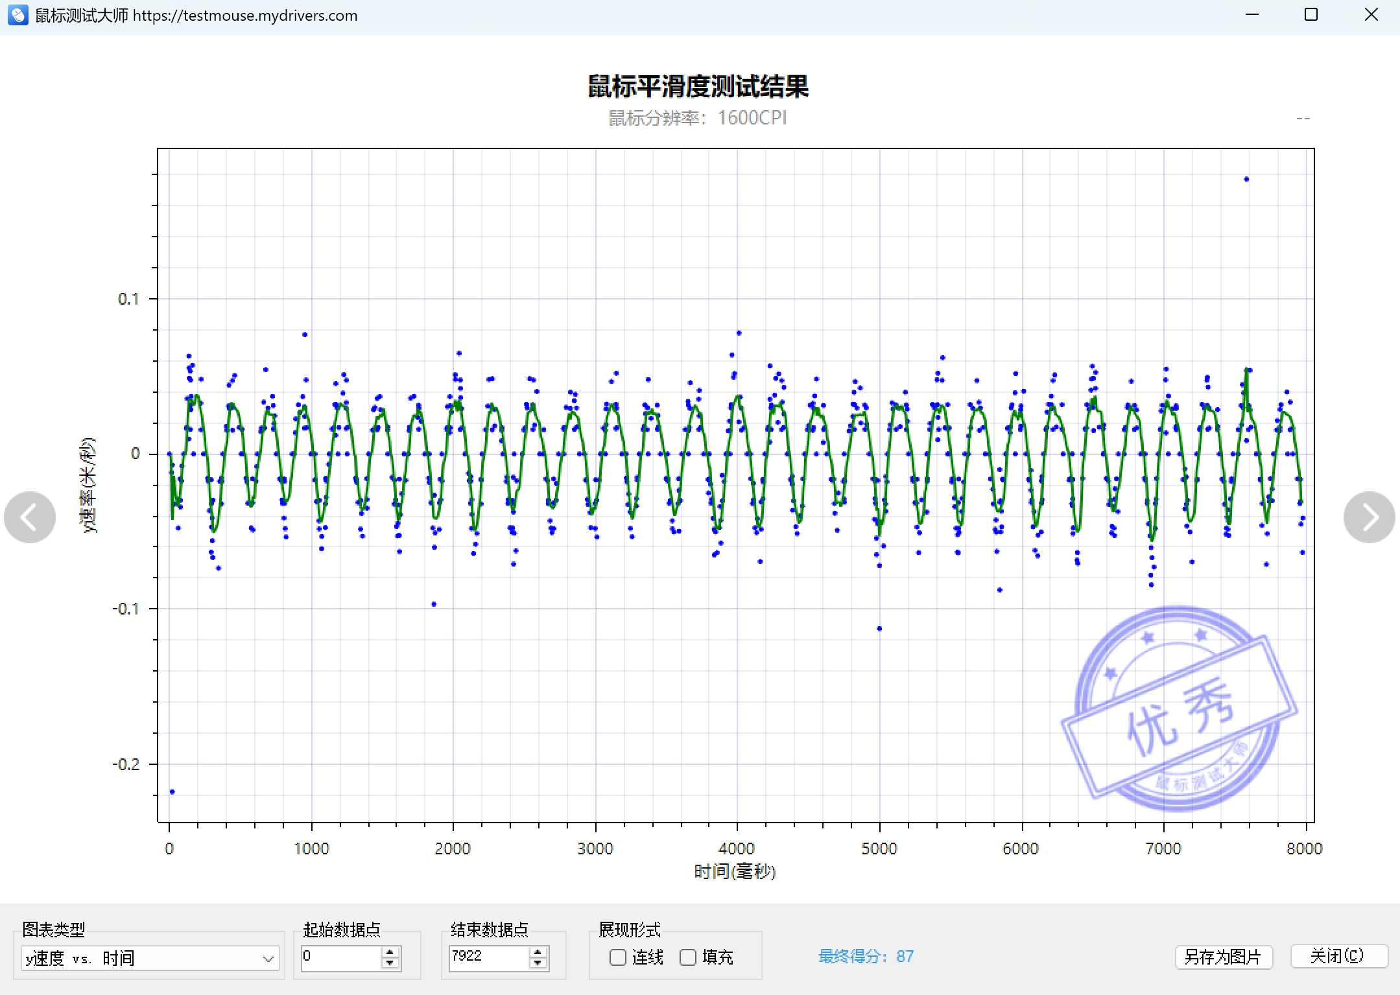
assets/usb_test/ySpeed_vs_Time.png
